CorvusPrudens/Oven-Controller/software/img_to_bitmap/data/1bit.png

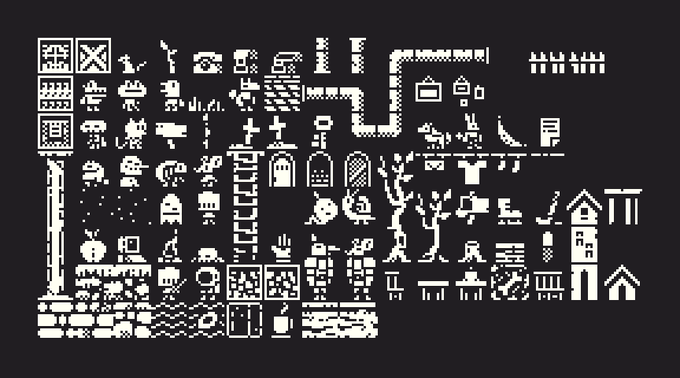
software/img_to_bitmap/data/1bit.png
