CorvusPrudens/Oven-Controller/software/img_to_bitmap/data/bisheet2.webp

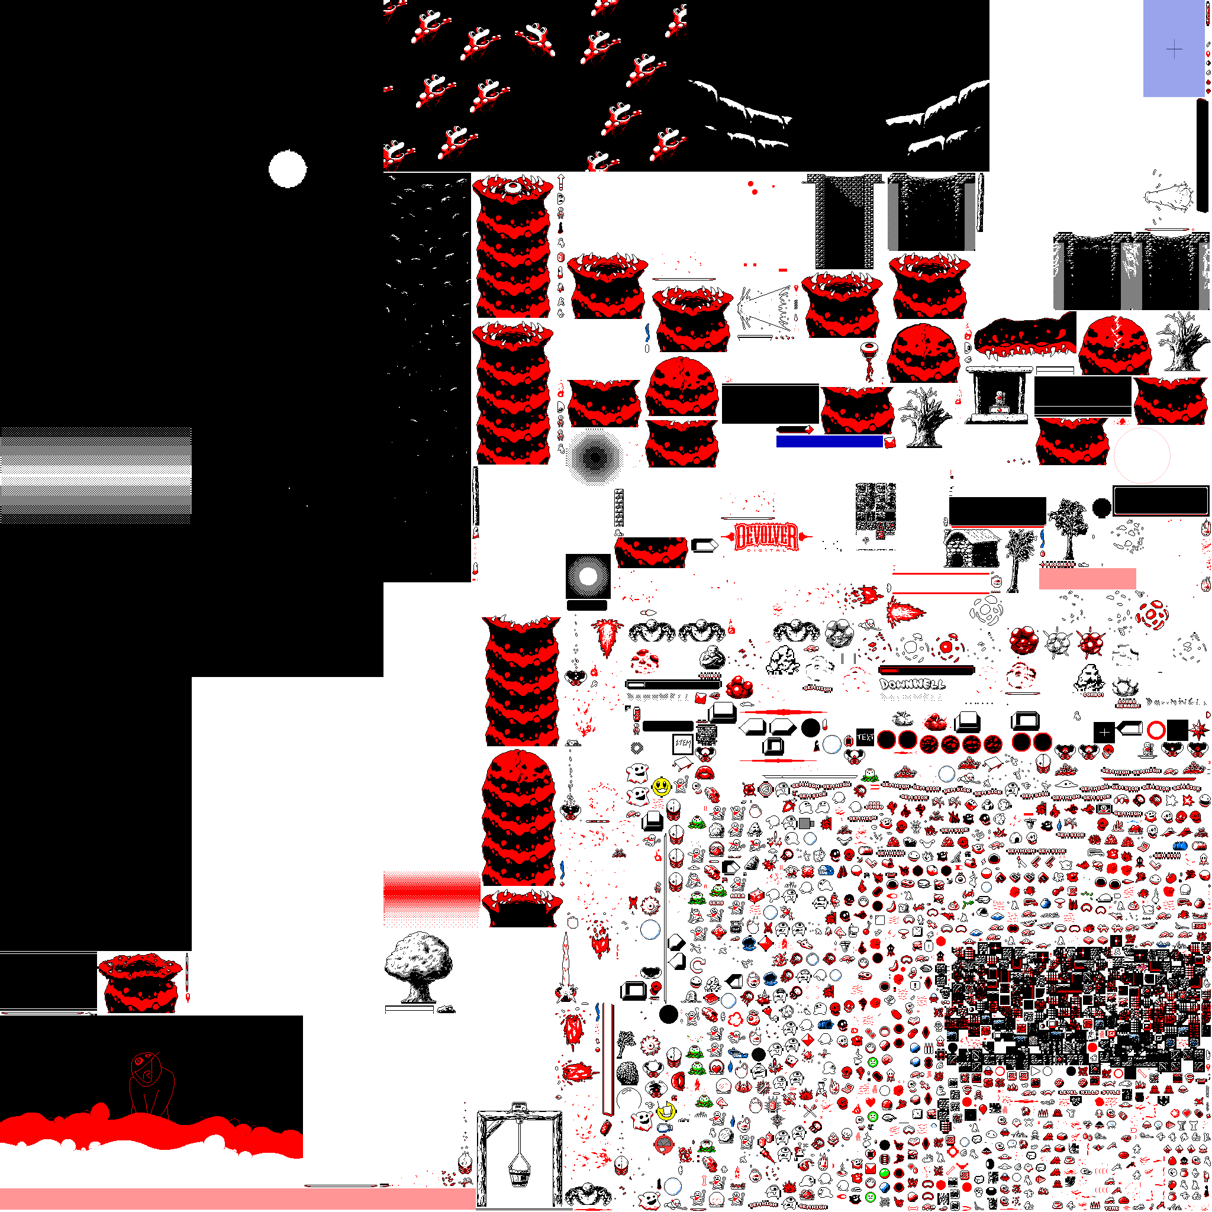
software/img_to_bitmap/data/bisheet2.webp
