CorvusPrudens/Oven-Controller/software/img_to_bitmap/data/leaves.webp

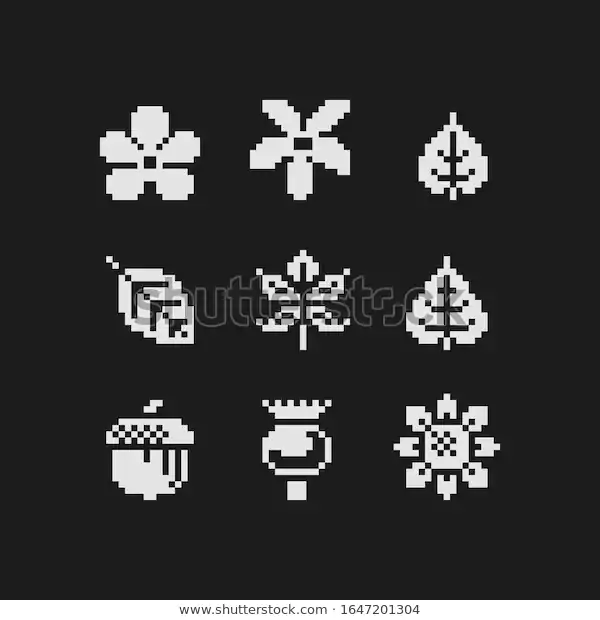
software/img_to_bitmap/data/leaves.webp
