CorvusPrudens/Oven-Controller/software/img_to_bitmap/data/maybemaybe.png

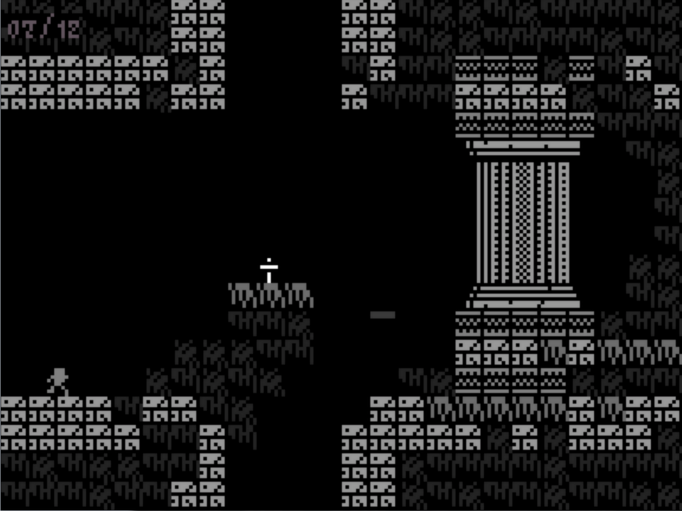
software/img_to_bitmap/data/maybemaybe.png
