CorvusPrudens/Oven-Controller/software/img_to_bitmap/data/menu.jpg

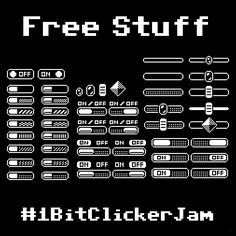
software/img_to_bitmap/data/menu.jpg
