CorvusPrudens/Oven-Controller/software/img_to_bitmap/data/niceTileset.gif

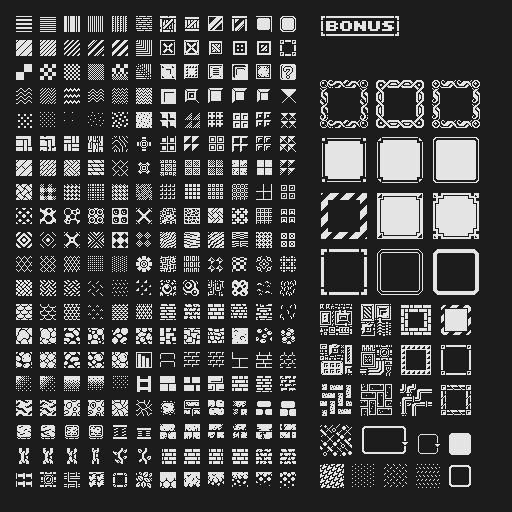
software/img_to_bitmap/data/niceTileset.gif
