CorvusPrudens/Oven-Controller/software/img_to_bitmap/data/plants.png

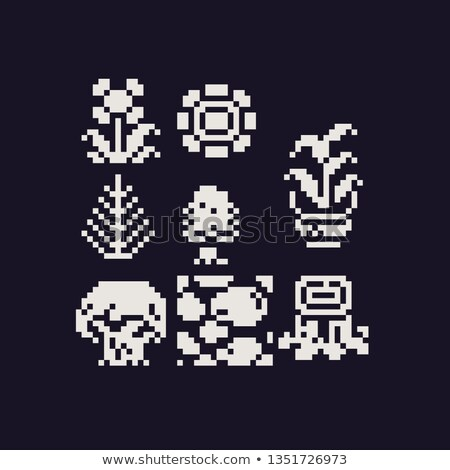
software/img_to_bitmap/data/plants.png
