CorvusPrudens/Oven-Controller/software/img_to_bitmap/data/things.png

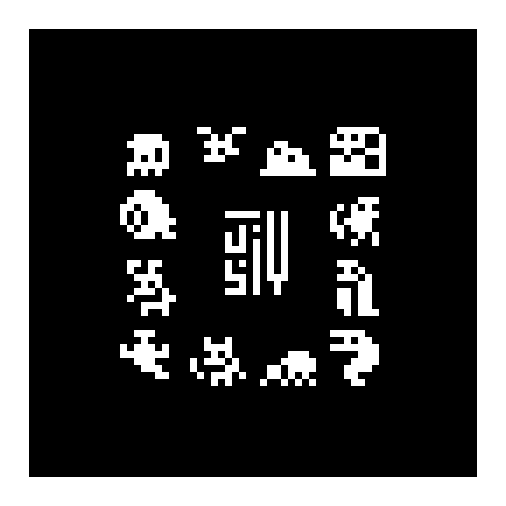
software/img_to_bitmap/data/things.png
