CorvusPrudens/Oven-Controller/software/img_to_bitmap/data/uwu.png

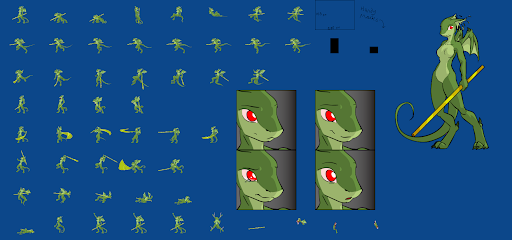
software/img_to_bitmap/data/uwu.png
