CorvusPrudens/Oven-Controller/firmware/bitmaps.h

const byte blockbm[] PROGMEM = {
  0xEA, 0x0B, 0x23, 0x32, 0x1B, 0x02, 0x92, 0xB4, 0x3A, 0x13, 0x03, 0x29, 0x61,
  0x65,
  0x0C, 0x1C, 0x08, 0x00, 0x06, 0x33, 0x33, 0x03, 0x00, 0x28, 0x19, 0x19, 0x00,
  0x0A
};

const byte torches[] PROGMEM = {
  // Bitmap 0 (0, 0)
  0x00, 0xEC, 0xFC, 0xF8, 0xC0, 0x00,
  0x00, 0x3B, 0xFF, 0xFD, 0x63, 0x00,
  0x00, 0x00, 0x01, 0x07, 0x00, 0x00,
  // Bitmap 1 (1, 0)
  0x80, 0xC2, 0xE2, 0xF0, 0xC0, 0x00,
  0x07, 0x3F, 0xFB, 0xFB, 0x67, 0x07,
  0x00, 0x00, 0x01, 0x07, 0x00, 0x00,
  // Bitmap 2 (2, 0)
  0x80, 0xC1, 0xE0, 0xF8, 0xC0, 0x00,
  0x03, 0x3F, 0xFB, 0xFB, 0x67, 0x03,
  0x00, 0x00, 0x01, 0x07, 0x00, 0x00
};

const byte ceiling[] PROGMEM = {
  0x00, 0x45, 0x00, 0x11, 0x00, 0x45, 0x00, 0x11, 0x00, 0x45, 0x00, 0x11, 0x00,
  0x45, 0x00, 0x11,
  0x00, 0x08, 0x00, 0x01, 0x00, 0x08, 0x00, 0x01, 0x00, 0x08, 0x00, 0x01, 0x00,
  0x08, 0x00, 0x01
};

const byte snowflake[] PROGMEM = {
  0x40, 0x60, 0x80, 0x10, 0xE0, 0x10, 0x80, 0x60, 0x40,
  0x04, 0x0D, 0x03, 0x11, 0x0F, 0x11, 0x03, 0x0D, 0x04,
};

const byte crumblingTile[] PROGMEM = {
  0x1F, 0x1F, 0x0D, 0xC3, 0xE7, 0xE7, 0xC3, 0x0D, 0x1F, 0x1F, 0x0F, 0xC3, 0xE7,
  0xE7, 0xC3, 0x0D,
  0x06, 0x04, 0x00, 0x00, 0x11, 0x01, 0x00, 0x00, 0x06, 0x02, 0x00, 0x00, 0x01,
  0x21, 0x00, 0x00
};

const byte columnbm[] PROGMEM = {
  0x53, 0x49, 0x53, 0x49, 0x53, 0x49, 0x53, 0x00, 0x53, 0x49, 0x53, 0x49, 0x53,
  0x49, 0x53, 0x00, 0x53, 0x49, 0x53, 0x49, 0x53, 0x49, 0x53, 0x00, 0x53, 0x49,
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
  0x00, 0x00, 0x00, 0x00, 0x00, 0x11, 0x17, 0x0F, 0x1F, 0x1B, 0x79, 0x61, 0x00, 0x00, 0x00, 0x00,
  // Bitmap 13 (1, 3)
  0x00, 0x00, 0x80, 0x80, 0x80, 0xC0, 0xC0, 0xE0, 0x20, 0xE0, 0x20, 0x00, 0x00, 0x00, 0x00, 0x00,
  0x00, 0x00, 0x01, 0x01, 0x03, 0xE7, 0xFF, 0xBF, 0x0F, 0x1F, 0x0F, 0x06, 0x04, 0x00, 0x00, 0x00
};
