CorvusPrudens/Oven-Controller/firmware/asongs.h

const byte blip[] PROGMEM = {
  1,
  7,
  2,
  12, 2,
  16, 2
};

const byte forward[] PROGMEM = {
  0,
  7,
  4,
  12, 1,
  14, 1,
  16, 1,
  24, 1
};

const byte back[] PROGMEM = {
  0,
  7,
  4,
  24, 1,
  16, 1,
  16, 1,
  12, 1
};

const byte mario[] PROGMEM = {
  0,
  2,
  105,
  16, 2,
  16, 2,
  255, 2,
  16, 2,
  255, 2,
  12, 2,
  16, 2,
  255, 2,
  19, 2,
  255, 6,
  7, 2,
  255, 6,
  12, 4,
  255, 2,
  7, 4,
  255, 2,
  4, 4,
  255, 2,
  9, 2,
  255, 2,
  11, 4,
  10, 2,
  9, 4,
  7, 3,
  16, 3,
  19, 2,
  21, 4,
  17, 2,
  19, 2,
  255, 2,
  16, 4,
  12, 2,
  14, 2,
  11, 4,
  255, 2,
  12, 4,
  255, 2,
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
};

const byte zelda[] PROGMEM = {
  0,
  1,
  120,
  21, 2,
  14, 2,
  10, 2,
  7, 2,
  19, 2,
  14, 2,
  10, 2,
  7, 2,
  18, 2,
  14, 2,
  10, 2,
  7, 2,
  19, 2,
  14, 2,
  10, 2,
  7, 2,
  19, 2,
  12, 2,
  9, 2,
  5, 2,
  17, 2,
  12, 2,
  9, 2,
  5, 2,
  16, 2,
  12, 2,
  9, 2,
  5, 2,
  17, 2,
  12, 2,
  9, 2,
  5, 2,
  17, 2,
  10, 2,
  7, 2,
  4, 2,
  16, 2,
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
};

const byte ff7myst[] PROGMEM = {
  0,
  1,
  9,
  24, 4,
  19, 4,
  23, 8,
  255, 16,
  22, 4,
  17, 4,
  21, 4,
  19, 8,
  255, 16
};

const byte ff7vict[] PROGMEM = {
  1,
  2,
  10,
  12, 2,
  12, 2,
  12, 2,
  12, 6,
  8, 6,
  10, 6,
  12, 4,
  10, 2,
  12, 12,
  255, 6
};

const byte mariovict[] PROGMEM = {
  1, // MODE
  3, // Tempo index
  28, // number of notes
  7, 2,
  12, 2,
  16, 2,
  19, 2,
  24, 2,
  28, 2,
  31, 6,
  28, 6,
  8, 2,
  12, 2,
  15, 2,
  20, 2,
  24, 2,
  27, 2,
  32, 6,
  27, 6,
  10, 2,
  14, 2,
  17, 2,
  22, 2,
  26, 2,
  29, 2,
  34, 6,
  34, 2,
  34, 2,
  34, 2,
  36, 14,
  255, 10
};
